MHaselmaier/modular-recon-drone/doc/imgs/camera_tcp_server.png

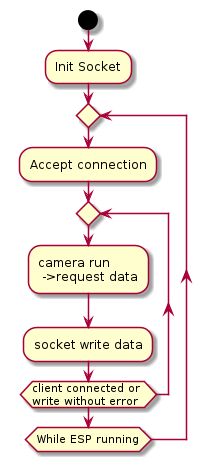
doc/imgs/camera_tcp_server.png
