MHaselmaier/modular-recon-drone/doc/imgs/display_update_diagram.png

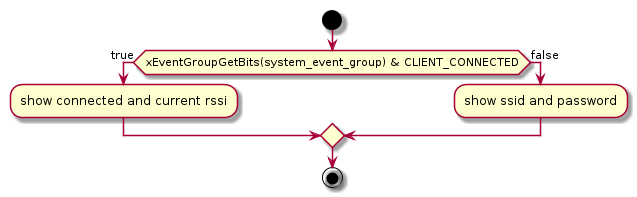
doc/imgs/display_update_diagram.png
