MHaselmaier/modular-recon-drone/doc/imgs/event_handling_diagram.png

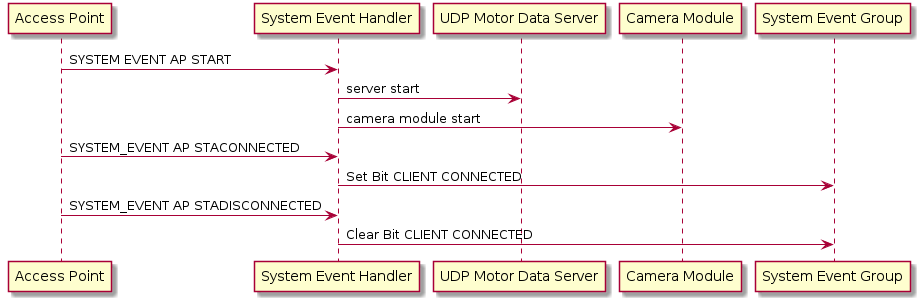
doc/imgs/event_handling_diagram.png
