MHaselmaier/modular-recon-drone/doc/imgs/motor_data_byte_layout.png

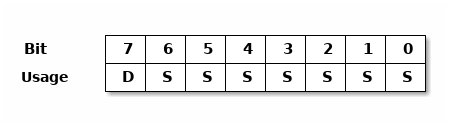
doc/imgs/motor_data_byte_layout.png
