MHaselmaier/modular-recon-drone/doc/imgs/udp-packet.png

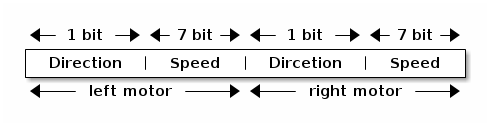
doc/imgs/udp-packet.png
