MHaselmaier/modular-recon-drone/main_control_unit/components/camera/wiring.h

#ifndef __OMV_PORT_H__
#define __OMV_PORT_H__

#include <freertos/FreeRTOS.h>
#include <freertos/task.h>


// Some functions from Arduino/Wiring
void pinMode(int pin, int mode);
void digitalWrite(int pin, int value);
void delay(int millis);

#define OUTPUT 0
#define INPUT 1
#define INPUT_PULLUP 2

// Some functions to make OpenMV happy
#define systick_sleep(t) delay(t)
#define __disable_irq()
#define __enable_irq()



#endif //__OMV_PORT_H__
